CombatCovid/mit-emergency-ventilator/docs/img/version-3/summary.jpg

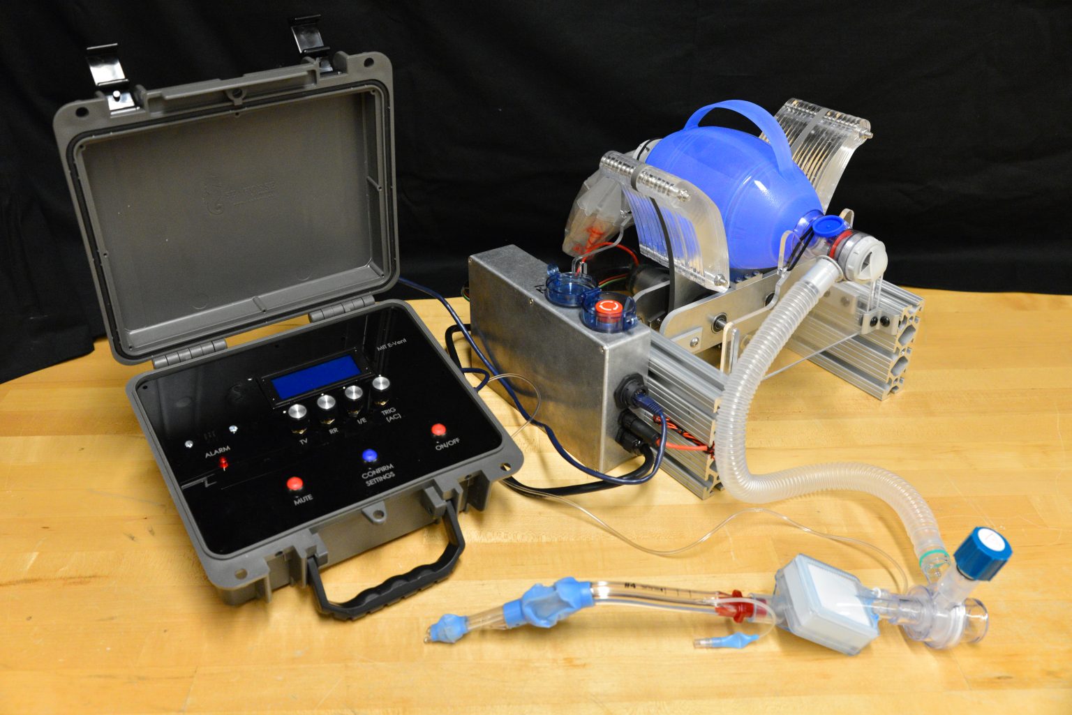
docs/img/version-3/summary.jpg
